KyleDavis2200/Keeboard/Firmware/boot.py

import supervisor
import board
import digitalio
import storage
import usb_cdc
import usb_hid

supervisor.set_next_stack_limit(4096+4096)

col = digitalio.DigitalInOut(board.GP0)
row = digitalio.DigitalInOut(board.GP22)

col.switch_to_output(value=True)
row.switch_to_input(pull=digitalio.Pull.DOWN)

if not row.value
    storage.disable_usb_drive()
    usb_cdc.disable()
    usb_hid.enable(boot_device=1)

row.deinit()
col.deinit()
